ReclaimerLabs/USB-C-Explorer/firmware/USB-C Explorer/USB-C Explorer/src/QTouch/QDebug_samd.h

/* This source file is part of the ATMEL QTouch Library 5.0.8 */

/*****************************************************************************
 *
 * \file
 *
 * \brief  This file contains the QDebug public API that can be used to
 * transfer data from a Touch Device to QTouch Studio using the QT600
 * USB Bridge.
 *
 *
 * - Userguide:          QTouch Library Peripheral Touch Controller User Guide.
 * - Support email:      www.atmel.com/design-support/
 *
 *
 * Copyright (c) 2013-2015 Atmel Corporation. All rights reserved.
 *
 * \asf_license_start
 *
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
 * 3. The name of Atmel may not be used to endorse or promote products derived
 *    from this software without specific prior written permission.
 *
 * 4. This software may only be redistributed and used in connection with an
 *    Atmel microcontroller product.
 *
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
 * \asf_license_stop
 *
 ******************************************************************************/

#ifndef _QDEBUG_SAMD_H_
#define _QDEBUG_SAMD_H_

#ifdef __cplusplus
extern "C"
{
#endif

/*============================ INCLUDES ======================================*/
#include "touch.h"
#include "touch_api_ptc.h"

/* ! compile file only when QDebug is enabled. */
#if DEF_TOUCH_QDEBUG_ENABLE == 1

/*======================== MANIFEST CONSTANTS ================================*/

/*! \name Subscription definitions.
 */
/* ! @{ */

#define SUBS_SIGN_ON            0
#define SUBS_GLOBAL_CONFIG      1
#define SUBS_SENSOR_CONFIG      2
#define SUBS_SIGNALS            3
#define SUBS_REF                4
#define SUBS_DELTA              5
#define SUBS_STATES             6

/* ! @} */

/*! \name PC commands.
 */
/* ! @{ */

#define QT_CMD_DUMMY                    0x10
#define QT_CMD_SET_SUBS                 0x11
#define QT_CMD_SET_GLOBAL_CONFIG        0x12
#define QT_CMD_SET_CH_CONFIG            0x13
#define QT_CMD_SET_MEASUREMENT_PERIOD   0x14
#define QT_CMD_SET_QM_BURST_LENGTHS     0x15

/* ! @} */

/*! \name Touch MCU data packets.
 */
/* ! @{ */

#define QT_DUMMY                                0x20
#define QT_SIGN_ON                              0x21
#define QT_GLOBAL_CONFIG                0x22
#define QT_SENSOR_CONFIG                0x23
#define QT_SIGNALS                              0x24
#define QT_REFERENCES                   0x25
#define QT_DELTAS                               0x26
#define QT_STATES                               0x27

/* ! @} */

/*============================ MACROS ========================================*/

/*! \name Macros for QTouch API and data structure.
 */
#ifdef DEF_TOUCH_QDEBUG_ENABLE_MUTLCAP

#define QDEBUG_SENSOR_STATES_PTR               p_mutlcap_measure_data->	\
	p_sensor_states
#define QDEBUG_SENSOR_PTR                          p_mutlcap_measure_data-> \
	p_sensors
#define QDEBUG_SIGNALS_PTR                     p_mutlcap_measure_data->	\
	p_channel_signals
#define QDEBUG_REFERENCES_PTR                  p_mutlcap_measure_data->	\
	p_channel_references
#define QDEBUG_SENSOR_RS_VALUES                p_mutlcap_measure_data->	\
	p_rotor_slider_values
#define QDEBUG_LIBINFO                         qt_touch_libver_info
#define QDEBUG_NUM_SENSOR_STATE_BYTES          ((DEF_MUTLCAP_NUM_CHANNELS + \
	7u) / 8u)
#define QDEBUG_GET_DELTA_FUNC(x, y)             touch_mutlcap_sensor_get_delta(	\
		x, y)
#define QDEBUG_GET_LIBINFO_FUNC(x)             touch_library_get_version_info(x)
#define QDEBUG_GET_GLOBAL_PARAM_FUNC(x)        touch_mutlcap_get_global_param(x)
#define QDEBUG_UPDATE_GLOBAL_PARAM_FUNC(x)     touch_mutlcap_update_global_param( \
		x)
#define QDEBUG_GET_SENSOR_CONFIG_FUNC(x, y)     touch_mutlcap_sensor_get_config( \
		x, y)
#define QDEBUG_UPDATE_SENSOR_CONFIG_FUNC(x, \
			y)  touch_mutlcap_sensor_update_config(x, y)
#define QDEBUG_NUM_SENSORS                     DEF_MUTLCAP_NUM_SENSORS
#define QDEBUG_NUM_CHANNELS                    DEF_MUTLCAP_NUM_CHANNELS
#define QDEBUG_NUM_ROTORS_SLIDERS              DEF_MUTLCAP_NUM_ROTORS_SLIDERS

#endif

#ifdef DEF_TOUCH_QDEBUG_ENABLE_SELFCAP
#define QDEBUG_SENSOR_STATES_PTR               p_selfcap_measure_data->	\
	p_sensor_states
#define QDEBUG_SENSOR_PTR                          p_selfcap_measure_data-> \
	p_sensors
#define QDEBUG_SIGNALS_PTR                     p_selfcap_measure_data->	\
	p_channel_signals
#define QDEBUG_REFERENCES_PTR                  p_selfcap_measure_data->	\
	p_channel_references
#define QDEBUG_SENSOR_RS_VALUES                p_selfcap_measure_data->	\
	p_rotor_slider_values
#define QDEBUG_LIBINFO                         qt_touch_libver_info
#define QDEBUG_NUM_SENSOR_STATE_BYTES          ((DEF_SELFCAP_NUM_CHANNELS + \
	7u) / 8u)
#define QDEBUG_GET_DELTA_FUNC(x, y)             touch_selfcap_sensor_get_delta(	\
		x, y)
#define QDEBUG_GET_LIBINFO_FUNC(x)             touch_library_get_version_info(x)
#define QDEBUG_GET_GLOBAL_PARAM_FUNC(x)        touch_selfcap_get_global_param(x)
#define QDEBUG_UPDATE_GLOBAL_PARAM_FUNC(x)     touch_selfcap_update_global_param( \
		x)
#define QDEBUG_GET_SENSOR_CONFIG_FUNC(x, y)     touch_selfcap_sensor_get_config( \
		x, y)
#define QDEBUG_UPDATE_SENSOR_CONFIG_FUNC(x, \
			y)  touch_selfcap_sensor_update_config(x, y)
#define QDEBUG_NUM_SENSORS                     DEF_SELFCAP_NUM_SENSORS
#define QDEBUG_NUM_CHANNELS                    DEF_SELFCAP_NUM_CHANNELS
#define QDEBUG_NUM_ROTORS_SLIDERS              DEF_SELFCAP_NUM_ROTORS_SLIDERS
#endif

/*======================== EXTERN VARIABLES ==================================*/
/* ! QTouch measured data pointer. */
/* extern touch_measure_data_t *p_qt_measure_data; */

/*============================ PROTOTYPES ====================================*/

/*! \name Public functions.
 */
/* ! @{ */

/*! \brief This API initializes QDebug interface, including the low level
 * hardware interface (SPI, TWI, USART etc).
 * \note Must be called before using any other QDebug API.
 */
void QDebug_Init(void);

/*! \brief Command handler for the data received from QTouch Studio
 * \note This function should be called in the main loop after
 * measure_sensors to process the data received from QTOuch Studio.
 */
void QDebug_ProcessCommands(void);

/*! \brief Send data to QTouch Studio based on the subscription.
 * \param  qt_lib_flags:Change flag from measure_sensors.
 */
void QDebug_SendData(uint16_t qt_lib_flags);

/*! \brief Set subscription values.
 * \note  This function can be used directly in main to set data subscription
 * if 1way SPI interface is used.
 */
void QDebug_SetSubscriptions(uint16_t once, uint16_t change,
		uint16_t allways);

/* ! @} */

/*! \name Private functions.
 */
/* ! @{ */

/*! \brief Extract the data packet from QTouch Studio and set global config.
 * \note  Should only be called from the command handler.
 */
void Set_Global_Config(void);

/*! \brief Extract the data packet from QTouch Studio and set channel config.
 * \note  Should only be called from the command handler.
 */
void Set_Channel_Config(void);

/*! \brief Set Data Subscription values.
 * \note  Should only be called from the command handler.
 */
void Set_Subscriptions(void);

/*! \brief Extract the data packet from QTouch Studio and set measurement
 * period.
 * \note  Should only be called from the command handler.
 */
void Set_Measurement_Period(void);

/*! \brief Extract the data packet from QTouch Studio and set QMatrix burst
 * lengths.
 * \note  Should only be called from the command handler.
 */
void Set_QM_Burst_Lengths(void);

/*! \brief Extracts user data from QTouch Studio to touch mcu memory.
 * \param pdata: data pointer.
 * \note  The data can be binary data.
 */
void Set_QT_User_Data(uint8_t *pdata);

/*! \brief Transmits a dummy packet if no other subscriptions are set.
 */
void Transmit_Dummy(void);

/*! \brief Transmits the sign on packet to QTouch Studio.
 */
void Transmit_Sign_On(void);

/*! \brief Transmits the global config struct to QTouch Studio.
 */
void Transmit_Global_Config(void);

/*! \brief Transmits the channel config struct to QTouch Studio.
 */
void Transmit_Sensor_Config(void);

/*! \brief Transmits the measurement values for each channel to QTouch Studio.
 */
void Transmit_Signals(void);

/*! \brief Transmits the channel reference values to QTouch Studio.
 */
void Transmit_Ref(void);

/*! \brief Transmits the channel delta values to QTouch Studio.
 */
void Transmit_Delta(void);

/*! \brief Transmits the state values to QTouch Studio.
 */
void Transmit_State(void);

/*! \brief Transmits the application execution timestamp values to QTouch
 * Studio.
 * \note This value is a combination of current_time_ms_touch (high word) &
 * timer counter register (low word).
 */
void Transmit_Time_Stamps(void);

/*! \brief Transmits user data to QTouch Studio.
 * \param pdata: data pointer.
 * \param c: length of data in bytes.
 * \note The data will be binary data.
 */
void Transmit_QT_User_Data(uint8_t *pdata, uint16_t c);

/* ! @} */

#endif  /* DEF_TOUCH_QDEBUG_ENABLE == 1 */

#ifdef __cplusplus
}
#endif

#endif /* _QDEBUG_SAMD_H_ */
/* EOF */
